OzmoOzmo/CastleHKCArduinoESP32/CastleHKCArduinoESP32/src/SoftwareSerial.h

/*
SoftwareSerial.h

SoftwareSerial.cpp - Implementation of the Arduino software serial for ESP8266/ESP32.
Copyright (c) 2015-2016 Peter Lerup. All rights reserved.
Copyright (c) 2018-2019 Dirk O. Kaar. All rights reserved.

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
*/

#ifndef __SoftwareSerial_h
#define __SoftwareSerial_h

#include "circular_queue/circular_queue.h"
#include <Stream.h>

enum SoftwareSerialParity : uint8_t {
    SWSERIAL_PARITY_NONE = 000,
    SWSERIAL_PARITY_EVEN = 020,
    SWSERIAL_PARITY_ODD = 030,
    SWSERIAL_PARITY_MARK = 040,
    SWSERIAL_PARITY_SPACE = 070,
};

enum SoftwareSerialConfig {
    SWSERIAL_5N1 = SWSERIAL_PARITY_NONE,
    SWSERIAL_6N1,
    SWSERIAL_7N1,
    SWSERIAL_8N1,
    SWSERIAL_5E1 = SWSERIAL_PARITY_EVEN,
    SWSERIAL_6E1,
    SWSERIAL_7E1,
    SWSERIAL_8E1,
    SWSERIAL_5O1 = SWSERIAL_PARITY_ODD,
    SWSERIAL_6O1,
    SWSERIAL_7O1,
    SWSERIAL_8O1,
    SWSERIAL_5M1 = SWSERIAL_PARITY_MARK,
    SWSERIAL_6M1,
    SWSERIAL_7M1,
    SWSERIAL_8M1,
    SWSERIAL_5S1 = SWSERIAL_PARITY_SPACE,
    SWSERIAL_6S1,
    SWSERIAL_7S1,
    SWSERIAL_8S1,
    SWSERIAL_5N2 = 0200 | SWSERIAL_PARITY_NONE,
    SWSERIAL_6N2,
    SWSERIAL_7N2,
    SWSERIAL_8N2,
    SWSERIAL_5E2 = 0200 | SWSERIAL_PARITY_EVEN,
    SWSERIAL_6E2,
    SWSERIAL_7E2,
    SWSERIAL_8E2,
    SWSERIAL_5O2 = 0200 | SWSERIAL_PARITY_ODD,
    SWSERIAL_6O2,
    SWSERIAL_7O2,
    SWSERIAL_8O2,
    SWSERIAL_5M2 = 0200 | SWSERIAL_PARITY_MARK,
    SWSERIAL_6M2,
    SWSERIAL_7M2,
    SWSERIAL_8M2,
    SWSERIAL_5S2 = 0200 | SWSERIAL_PARITY_SPACE,
    SWSERIAL_6S2,
    SWSERIAL_7S2,
    SWSERIAL_8S2,
};

/// This class is compatible with the corresponding AVR one, however,
/// the constructor takes no arguments, for compatibility with the
/// HardwareSerial class.
/// Instead, the begin() function handles pin assignments and logic inversion.
/// It also has optional input buffer capacity arguments for byte buffer and ISR bit buffer.
/// Bitrates up to at least 115200 can be used.
class SoftwareSerial : public Stream {
public:
    SoftwareSerial();
    /// Ctor to set defaults for pins.
    /// @param rxPin the GPIO pin used for RX
    /// @param txPin -1 for onewire protocol, GPIO pin used for twowire TX
    SoftwareSerial(int8_t rxPin, int8_t txPin = -1, bool invert = false);
    SoftwareSerial(const SoftwareSerial&) = delete;
    SoftwareSerial& operator= (const SoftwareSerial&) = delete;
    virtual ~SoftwareSerial();
    /// Configure the SoftwareSerial object for use.
    /// @param baud the TX/RX bitrate
    /// @param config sets databits, parity, and stop bit count
    /// @param rxPin -1 or default: either no RX pin, or keeps the rxPin set in the ctor
    /// @param txPin -1 or default: either no TX pin (onewire), or keeps the txPin set in the ctor
    /// @param invert true: uses invert line level logic
    /// @param bufCapacity the capacity for the received bytes buffer
    /// @param isrBufCapacity 0: derived from bufCapacity. The capacity of the internal asynchronous
    ///        bit receive buffer, a suggested size is bufCapacity times the sum of
    ///        start, data, parity and stop bit count.
    void begin(uint32_t baud, SoftwareSerialConfig config,
        int8_t rxPin, int8_t txPin, bool invert,
        int bufCapacity = 64, int isrBufCapacity = 0);
    void begin(uint32_t baud, SoftwareSerialConfig config,
        int8_t rxPin, int8_t txPin) {
        begin(baud, config, rxPin, txPin, m_invert);
    }
    void begin(uint32_t baud, SoftwareSerialConfig config,
        int8_t rxPin) {
        begin(baud, config, rxPin, m_txPin, m_invert);
    }
    void begin(uint32_t baud, SoftwareSerialConfig config = SWSERIAL_8N1) {
        begin(baud, config, m_rxPin, m_txPin, m_invert);
    }

    uint32_t baudRate();
    /// Transmit control pin.
    void setTransmitEnablePin(int8_t txEnablePin);
    /// Enable (default) or disable interrupts during tx.
    void enableIntTx(bool on);
    /// Enable (default) or disable internal rx GPIO pull-up.
    void enableRxGPIOPullUp(bool on);
    /// Enable or disable (default) tx GPIO output mode.
    void enableTxGPIOOpenDrain(bool on);

    bool overflow();

    int available() override;
#if defined(ESP8266)
    int availableForWrite() override {
#else
    int availableForWrite() {
#endif
        if (!m_txValid) return 0;
        return 1;
    }
    int peek() override;
    int read() override;
    /// @returns The verbatim parity bit associated with the last successful read() or peek() call
    bool readParity()
    {
        return m_lastReadParity;
    }
    /// @returns The calculated bit for even parity of the parameter byte
    static bool parityEven(uint8_t byte) {
        byte ^= byte >> 4;
        byte &= 0xf;
        return (0x6996 >> byte) & 1;
    }
    /// @returns The calculated bit for odd parity of the parameter byte
    static bool parityOdd(uint8_t byte) {
        byte ^= byte >> 4;
        byte &= 0xf;
        return (0x9669 >> byte) & 1;
    }
    /// The read(buffer, size) functions are non-blocking, the same as readBytes but without timeout
    int read(uint8_t* buffer, size_t size)
#if defined(ESP8266)
        override
#endif
        ;
    /// The read(buffer, size) functions are non-blocking, the same as readBytes but without timeout
    int read(char* buffer, size_t size) {
        return read(reinterpret_cast<uint8_t*>(buffer), size);
    }
    /// @returns The number of bytes read into buffer, up to size. Times out if the limit set through
    ///          Stream::setTimeout() is reached.
    size_t readBytes(uint8_t* buffer, size_t size) override;
    /// @returns The number of bytes read into buffer, up to size. Times out if the limit set through
    ///          Stream::setTimeout() is reached.
    size_t readBytes(char* buffer, size_t size) override {
        return readBytes(reinterpret_cast<uint8_t*>(buffer), size);
    }
    void flush() override;
    size_t write(uint8_t byte) override;
    size_t write(uint8_t byte, SoftwareSerialParity parity);
    size_t write(const uint8_t* buffer, size_t size) override;
    size_t write(const char* buffer, size_t size) {
        return write(reinterpret_cast<const uint8_t*>(buffer), size);
    }
    size_t write(const uint8_t* buffer, size_t size, SoftwareSerialParity parity);
    size_t write(const char* buffer, size_t size, SoftwareSerialParity parity) {
        return write(reinterpret_cast<const uint8_t*>(buffer), size, parity);
    }
    operator bool() const {
        return (-1 == m_rxPin || m_rxValid) && (-1 == m_txPin || m_txValid) && !(-1 == m_rxPin && m_oneWire);
    }

    /// Disable or enable interrupts on the rx pin.
    void enableRx(bool on);
    /// One wire control.
    void enableTx(bool on);

    // AVR compatibility methods.
    bool listen() { enableRx(true); return true; }
    void end();
    bool isListening() { return m_rxEnabled; }
    bool stopListening() { enableRx(false); return true; }

    /// onReceive sets a callback that will be called in interrupt context
    /// when data is received.
    /// More precisely, the callback is triggered when EspSoftwareSerial detects
    /// a new reception, which may not yet have completed on invocation.
    /// Reading - never from this interrupt context - should therefore be
    /// delayed for the duration of one incoming word.
    void onReceive(Delegate<void(), void*> handler);

    using Print::write;

private:
    // It's legal to exceed the deadline, for instance,
    // by enabling interrupts.
    void lazyDelay();
    // Synchronous precise delay
    void preciseDelay();
    // If withStopBit is set, either cycle contains a stop bit.
    // If dutyCycle == 0, the level is not forced to HIGH.
    // If offCycle == 0, the level remains unchanged from dutyCycle.
    void writePeriod(
        uint32_t dutyCycle, uint32_t offCycle, bool withStopBit);
    static constexpr bool isValidGPIOpin(int8_t pin);
    static constexpr bool isValidRxGPIOpin(int8_t pin);
    static constexpr bool isValidTxGPIOpin(int8_t pin);
    // result is only defined for a valid Rx GPIO pin
    static constexpr bool hasRxGPIOPullUp(int8_t pin);
    // safely set the pin mode for the Rx GPIO pin
    void setRxGPIOPinMode();
    // safely set the pin mode for the Tx GPIO pin
    void setTxGPIOPinMode();
    /* check m_rxValid that calling is safe */
    void rxBits();
    void rxBits(const uint32_t isrTick);
    static void disableInterrupts();
    static void restoreInterrupts();

    static void rxBitISR(SoftwareSerial* self);

    static inline uint32_t microsToTicks(uint32_t micros) {
        return micros << 1;
    }
    static inline uint32_t ticksToMicros(uint32_t ticks) {
        return ticks >> 1;
    }

    // Member variables
    int8_t m_rxPin = -1;
    volatile uint32_t* m_rxReg;
    uint32_t m_rxBitMask;
    int8_t m_txPin = -1;
#if !defined(ESP8266)
    volatile uint32_t* m_txReg;
#endif
    uint32_t m_txBitMask;
    int8_t m_txEnablePin = -1;
    uint8_t m_dataBits;
    bool m_oneWire;
    bool m_rxValid = false;
    bool m_rxEnabled = false;
    bool m_txValid = false;
    bool m_txEnableValid = false;
    bool m_invert;
    /// PDU bits include data, parity and stop bits; the start bit is not counted.
    uint8_t m_pduBits;
    bool m_intTxEnabled;
    bool m_rxGPIOPullUpEnabled;
    bool m_txGPIOOpenDrain;
    SoftwareSerialParity m_parityMode;
    uint8_t m_stopBits;
    bool m_lastReadParity;
    bool m_overflow = false;
    uint32_t m_bitTicks;
    uint8_t m_parityInPos;
    uint8_t m_parityOutPos;
    int8_t m_rxLastBit; // 0 thru (m_pduBits - m_stopBits - 1): data/parity bits. -1: start bit. (m_pduBits - 1): stop bit.
    uint8_t m_rxCurByte = 0;
    std::unique_ptr<circular_queue<uint8_t> > m_buffer;
    std::unique_ptr<circular_queue<uint8_t> > m_parityBuffer;
    uint32_t m_periodStart;
    uint32_t m_periodDuration;
#ifndef ESP32
    static uint32_t m_savedPS;
#else
    static portMUX_TYPE m_interruptsMux;
#endif
    // the ISR stores the relative bit times in the buffer. The inversion corrected level is used as sign bit (2's complement):
    // 1 = positive including 0, 0 = negative.
    std::unique_ptr<circular_queue<uint32_t, SoftwareSerial*> > m_isrBuffer;
    const Delegate<void(uint32_t&&), SoftwareSerial*> m_isrBufferForEachDel = { [](SoftwareSerial* self, uint32_t&& isrTick) { self->rxBits(isrTick); }, this };
    std::atomic<bool> m_isrOverflow;
    uint32_t m_isrLastTick;
    bool m_rxCurParity = false;
    Delegate<void(), void*> m_rxHandler;
};

#endif // __SoftwareSerial_h
