OzmoOzmo/CastleHKCArduinoESP32/CastleHKCArduinoESP32/src/OLEDDisplaySSD1306Wire.h

//A larger display library reduced in size to 3 files - AClarke Feb 2023

/**
 * The MIT License (MIT)
 *
 * Copyright (c) 2018 by ThingPulse, Daniel Eichhorn
 * Copyright (c) 2018 by Fabrice Weinberg
 *
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
 * ThingPulse invests considerable time and money to develop these open source libraries.
 * Please support us by buying our products (and not the clones) from
 * https://thingpulse.com
 *
 */

#ifndef SSD1306Wire_h
#define SSD1306Wire_h

#include "Arduino.h"

#include "OLEDDisplay.h"
#include <Wire.h>

#if defined(ARDUINO_ARCH_AVR) || defined(ARDUINO_ARCH_STM32)
#define _min	min
#define _max	max
#endif
//--------------------------------------

class SSD1306Wire : public OLEDDisplay {
  private:
      uint8_t             _address;
      int                 _sda;
      int                 _scl;
      bool                _doI2cAutoInit = false;
      TwoWire*            _wire = NULL;
      int                 _frequency;

  public:

    /**
     * Create and initialize the Display using Wire library
     *
     * Beware for retro-compatibility default values are provided for all parameters see below.
     * Please note that if you don't wan't SD1306Wire to initialize and change frequency speed ot need to 
     * ensure -1 value are specified for all 3 parameters. This can be usefull to control TwoWire with multiple
     * device on the same bus.
     * 
     * @param _address I2C Display address
     * @param _sda I2C SDA pin number, default to -1 to skip Wire begin call
     * @param _scl I2C SCL pin number, default to -1 (only SDA = -1 is considered to skip Wire begin call)
     * @param g display geometry dafault to generic GEOMETRY_128_64, see OLEDDISPLAY_GEOMETRY definition for other options
     * @param _i2cBus on ESP32 with 2 I2C HW buses, I2C_ONE for 1st Bus, I2C_TWO fot 2nd bus, default I2C_ONE
     * @param _frequency for Frequency by default Let's use ~700khz if ESP8266 is in 160Mhz mode, this will be limited to ~400khz if the ESP8266 in 80Mhz mode
     */
    SSD1306Wire(uint8_t _address, int _sda = -1, int _scl = -1, OLEDDISPLAY_GEOMETRY g = GEOMETRY_128_64, HW_I2C _i2cBus = I2C_ONE, unsigned int _frequency = 700000) {
      setGeometry(g);

      this->_address = _address;
      this->_sda = _sda;
      this->_scl = _scl;
#if !defined(ARDUINO_ARCH_ESP32)
      this->_wire = &Wire;
#else
      this->_wire = (_i2cBus==I2C_ONE) ? &Wire : &Wire1;
#endif
      this->_frequency = _frequency;
    }

    bool connect() {
#if !defined(ARDUINO_ARCH_ESP32) && !defined(ARDUINO_ARCH_ESP8266)
      _wire->begin();
#else
      // On ESP32 arduino, -1 means 'don't change pins', someone else has called begin for us.
      if(this->_sda != -1)
        _wire->begin(this->_sda, this->_scl);
#endif
      // Let's use ~700khz if ESP8266 is in 160Mhz mode
      // this will be limited to ~400khz if the ESP8266 in 80Mhz mode.
      if(this->_frequency != -1)
        _wire->setClock(this->_frequency);
      return true;
    }

    void display(void) {
      initI2cIfNeccesary();
      const int x_offset = (128 - this->width()) / 2;
      #ifdef OLEDDISPLAY_DOUBLE_BUFFER
        uint8_t minBoundY = UINT8_MAX;
        uint8_t maxBoundY = 0;

        uint8_t minBoundX = UINT8_MAX;
        uint8_t maxBoundX = 0;
        uint8_t x, y;

        // Calculate the Y bounding box of changes
        // and copy buffer[pos] to buffer_back[pos];
        for (y = 0; y < (this->height() / 8); y++) {
          for (x = 0; x < this->width(); x++) {
           uint16_t pos = x + y * this->width();
           if (buffer[pos] != buffer_back[pos]) {
             minBoundY = min(minBoundY, y);
             maxBoundY = max(maxBoundY, y);
             minBoundX = min(minBoundX, x);
             maxBoundX = max(maxBoundX, x);
           }
           buffer_back[pos] = buffer[pos];
         }
         yield();
        }

        // If the minBoundY wasn't updated
        // we can savely assume that buffer_back[pos] == buffer[pos]
        // holdes true for all values of pos

        if (minBoundY == UINT8_MAX) return;

        sendCommand(COLUMNADDR);
        sendCommand(x_offset + minBoundX);
        sendCommand(x_offset + maxBoundX);

        sendCommand(PAGEADDR);
        sendCommand(minBoundY);
        sendCommand(maxBoundY);

        byte k = 0;
        for (y = minBoundY; y <= maxBoundY; y++) {
          for (x = minBoundX; x <= maxBoundX; x++) {
            if (k == 0) {
              _wire->beginTransmission(_address);
              _wire->write(0x40);
            }

            _wire->write(buffer[x + y * this->width()]);
            k++;
            if (k == 16)  {
              _wire->endTransmission();
              k = 0;
            }
          }
          yield();
        }

        if (k != 0) {
          _wire->endTransmission();
        }
      #else

        sendCommand(COLUMNADDR);
        sendCommand(x_offset);
        sendCommand(x_offset + (this->width() - 1));

        sendCommand(PAGEADDR);
        sendCommand(0x0);

        for (uint16_t i=0; i < displayBufferSize; i++) {
          _wire->beginTransmission(this->_address);
          _wire->write(0x40);
          for (uint8_t x = 0; x < 16; x++) {
            _wire->write(buffer[i]);
            i++;
          }
          i--;
          _wire->endTransmission();
        }
      #endif
    }

    void setI2cAutoInit(bool doI2cAutoInit) {
      _doI2cAutoInit = doI2cAutoInit;
    }

  private:
	int getBufferOffset(void) {
		return 0;
	}
    inline void sendCommand(uint8_t command) __attribute__((always_inline)){
      initI2cIfNeccesary();
      _wire->beginTransmission(_address);
      _wire->write(0x80);
      _wire->write(command);
      _wire->endTransmission();
    }

    void initI2cIfNeccesary() {
      if (_doI2cAutoInit) {
#if !defined(ARDUINO_ARCH_ESP32) && !defined(ARDUINO_ARCH_ESP8266)
      	_wire->begin();
#else
      	_wire->begin(this->_sda, this->_scl);
#endif
      }
    }

};

#endif
